chrisgilmerproj/neoclock/pictures/neoclock_color_scheme_1.jpg

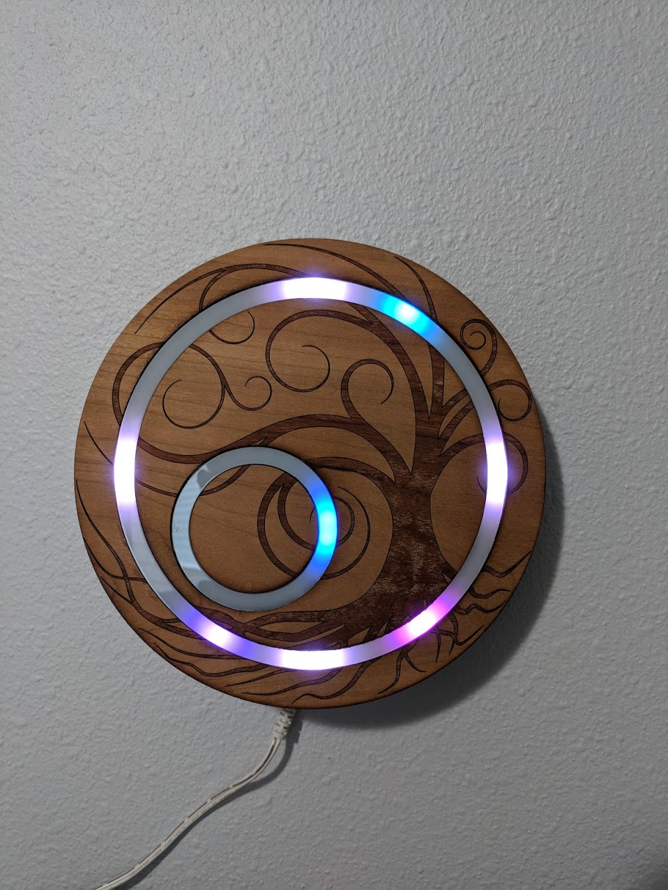
pictures/neoclock_color_scheme_1.jpg
