chrisgilmerproj/neoclock/ponoko/tree_research/celtic_tree_of_life.png

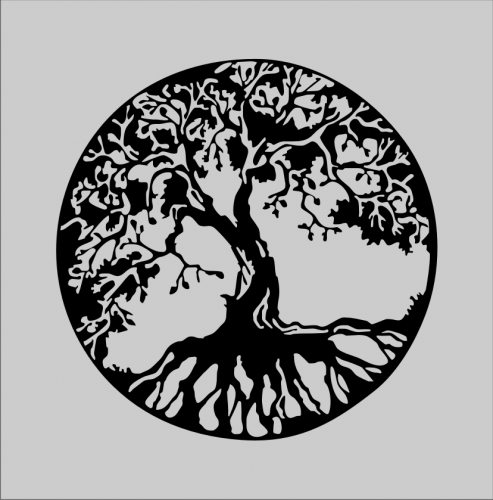
ponoko/tree_research/celtic_tree_of_life.png
