chrisgilmerproj/neoclock/ponoko/tree_research/circle tree 2.jpg

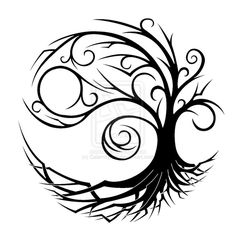
ponoko/tree_research/circle tree 2.jpg
