chrisgilmerproj/neoclock/ponoko/tree_research/Tree.JPG

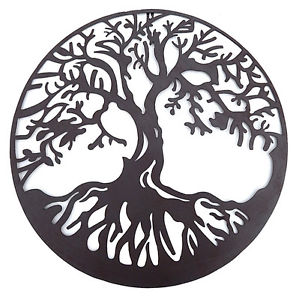
ponoko/tree_research/Tree.JPG
